vtolenti89/iot-watering-system/Simulation/water_sensor.asc

R1: res; {Rref}
R2: res; {Rref}
R3: res; {Rref}
R4: res; {Rref}
R5: res; {Rref}
S1: sw; MYSW1
S2: sw; MYSW2
S3: sw; MYSW3
S4: sw; MYSW4
S5: sw; MYSW5
V1: voltage; 5
V2: voltage; 1
Named nets: 0, ADC, V_W
.model MYSW1 SW(Ron={R_W1} Roff=1Meg Vt=0.9 )
.model MYSW2 SW(Ron={R_W2} Roff=1Meg Vt=1.9 )
.model MYSW3 SW(Ron={R_W3} Roff=1Meg Vt=2.9 )
.model MYSW4 SW(Ron={R_W4} Roff=1Meg Vt=3.9 )
.model MYSW5 SW(Ron={R_W5} Roff=1Meg Vt=4.9 )
.step param res_W list 20 2k
.step param Rref list 100k 200k
.param hMax 0.5
.param radius 0.05
.param area 3.1415*(radius**2)
.param R_W1 res_W/area*hMax/1
.param R_W2 res_W/area*hMax/2
.param R_W3 res_W/area*hMax/3
.param R_W4 res_W/area*hMax/4
.param R_W5 res_W/area*hMax/5
.dc V2 1 5 1
