vtolenti89/iot-watering-system/Simulation/water_sensor_2.asc

R1: res; 100k
R2: res; 20k
R3: res; 47k
R4: res; 68k
R5: res; 220k
S1: sw; MYSW1
S2: sw; MYSW2
S3: sw; MYSW3
S4: sw; MYSW4
S5: sw; MYSW5
V1: voltage; 5
V2: voltage; 1
Named nets: 0, ADC, V_W
.model MYSW1 SW(Ron={R_W1} Roff=100Meg Vt=0.9 )
.model MYSW2 SW(Ron={R_W2} Roff=100Meg Vt=1.9 )
.model MYSW3 SW(Ron={R_W3} Roff=100Meg Vt=2.9 )
.model MYSW4 SW(Ron={R_W4} Roff=100Meg Vt=3.9 )
.model MYSW5 SW(Ron={R_W5} Roff=100Meg Vt=4.9 )
.step param res_W list 20 2k
.step param Rref list 100k 200k
.param hMax 0.550
.param radius 0.19
.param area 3.1415*(radius**2)
.param R_W1 21k
.param R_W2 11.9k
.param R_W3 15.9k
.param R_W4 14.87k
.param R_W5 16.7k
.dc V2 0 5 1
